Zioto06/monitoramento-ambiental-ifes/monitoramento/PA3.sch

## EAGLE design monitoramento/PA3.sch (2025-11-21)

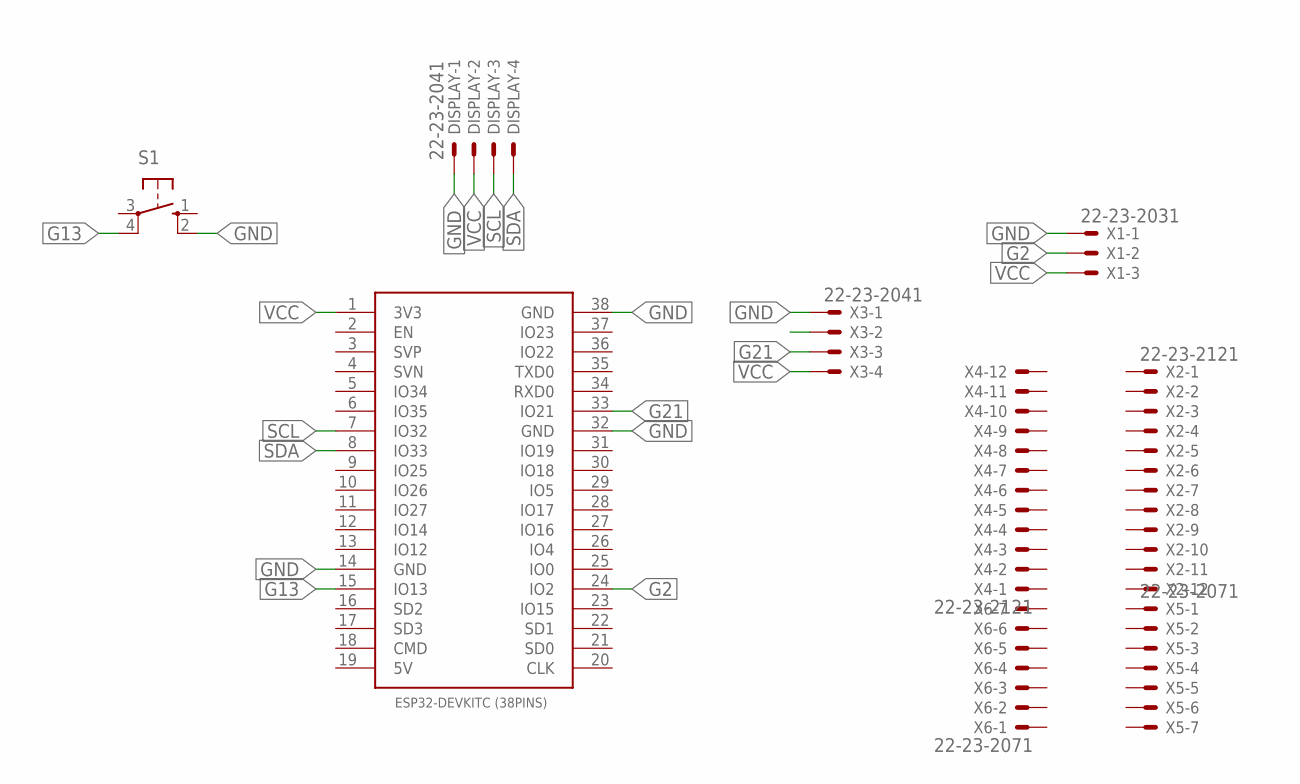
[picture p4: schematic PA3.sch]

Parts:
DISPLAY: 22-23-2041
ESP32-DEVKITC(38PINS)1: ESP32DEVKITC_38PINS; ESP32-DEVKITC
S1: 10-XX; B3F-10XX
X1: 22-23-2031
X2, X4: 22-23-2121
X3: 22-23-2041
X5, X6: 22-23-2071

Connections:
G2: ESP32-DEVKITC(38PINS)1.24 (IO2), X1.2
G13: ESP32-DEVKITC(38PINS)1.15 (IO13), S1.4 (P1)
G21: ESP32-DEVKITC(38PINS)1.33 (IO21), X3.3
GND: DISPLAY.1, ESP32-DEVKITC(38PINS)1.14 (GND), ESP32-DEVKITC(38PINS)1.32 (GND), ESP32-DEVKITC(38PINS)1.38 (GND), S1.2 (S1), X1.1, X3.1
SCL: DISPLAY.3, ESP32-DEVKITC(38PINS)1.7 (IO32)
SDA: DISPLAY.4, ESP32-DEVKITC(38PINS)1.8 (IO33)
VCC: DISPLAY.2, ESP32-DEVKITC(38PINS)1.1 (3V3), X1.3, X3.4
